OtagoPolytechnic/DunedinIoT/images/20160920_135408.jpg

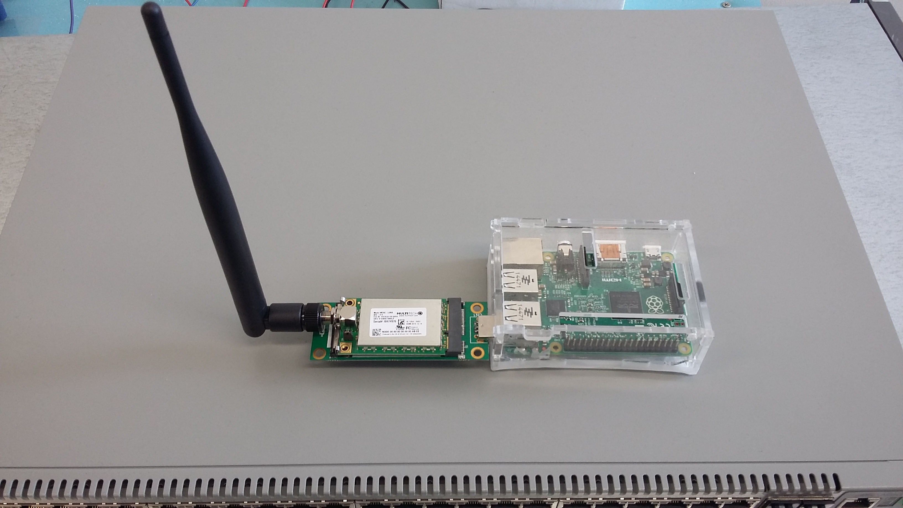
images/20160920_135408.jpg
