OtagoPolytechnic/DunedinIoT/images/20160920_135431.jpg

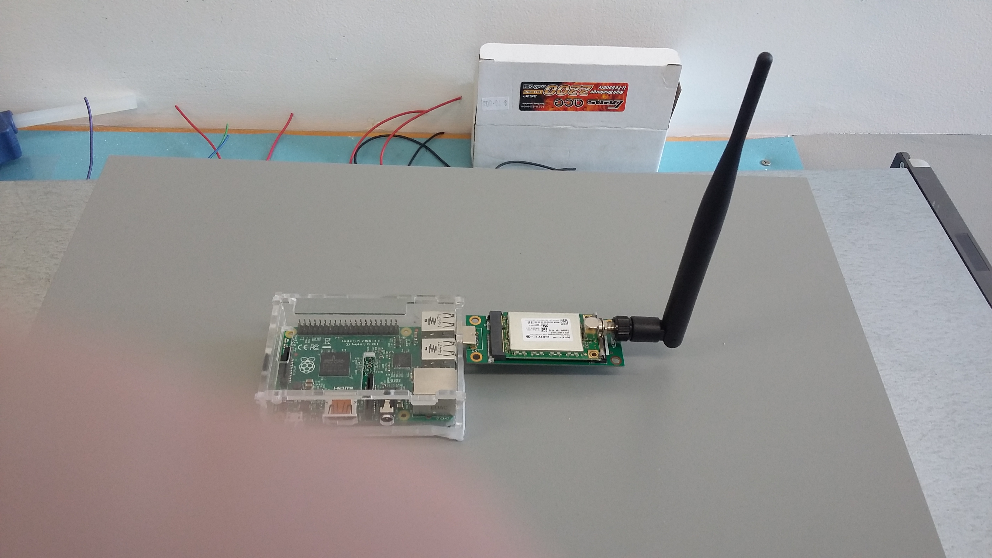
images/20160920_135431.jpg
