OtagoPolytechnic/DunedinIoT/images/20160920_135444.jpg

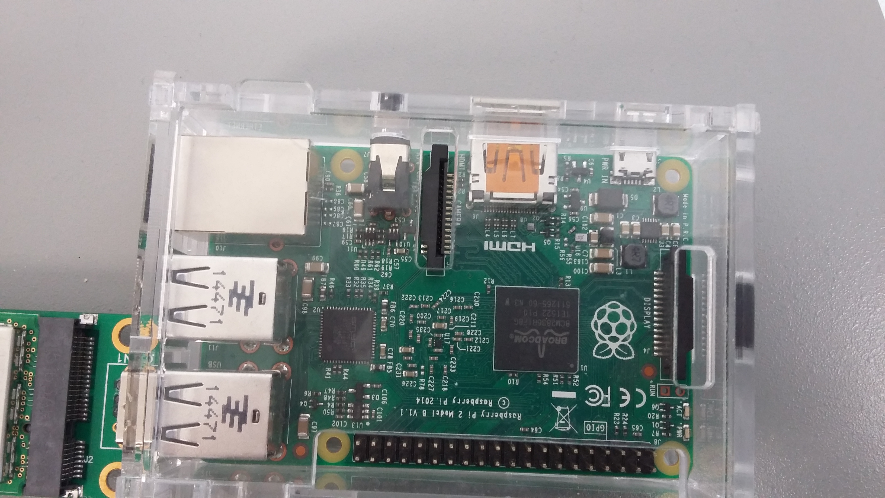
images/20160920_135444.jpg
