OtagoPolytechnic/DunedinIoT/images/20160920_135453.jpg

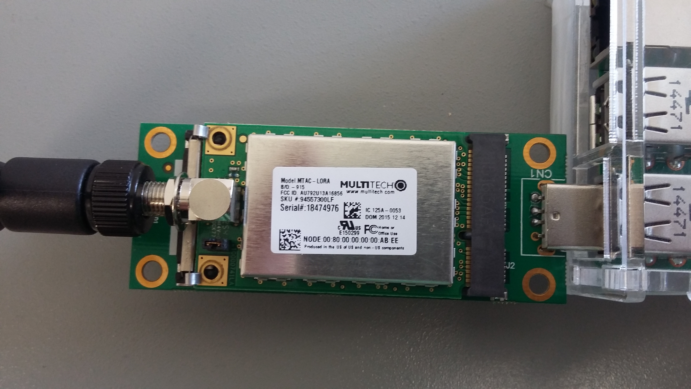
images/20160920_135453.jpg
