OtagoPolytechnic/DunedinIoT/images/20160920_135511.jpg

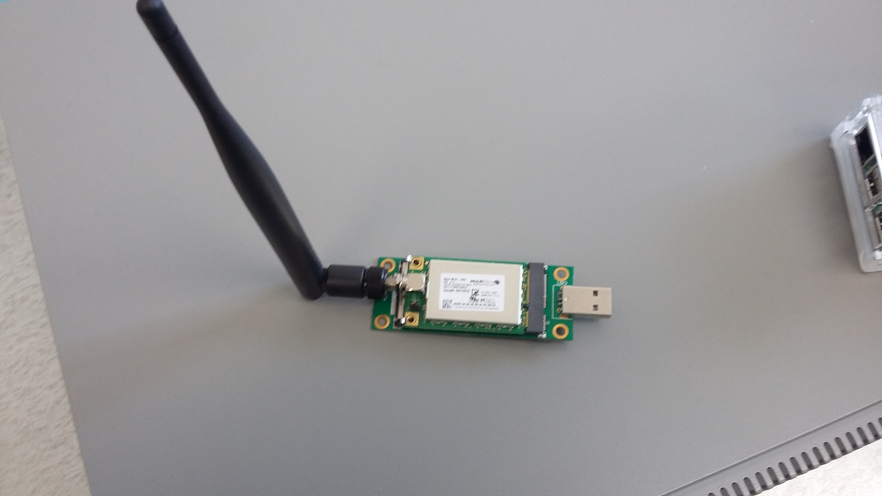
images/20160920_135511.jpg
