OtagoPolytechnic/DunedinIoT/images/20160920_135528.jpg

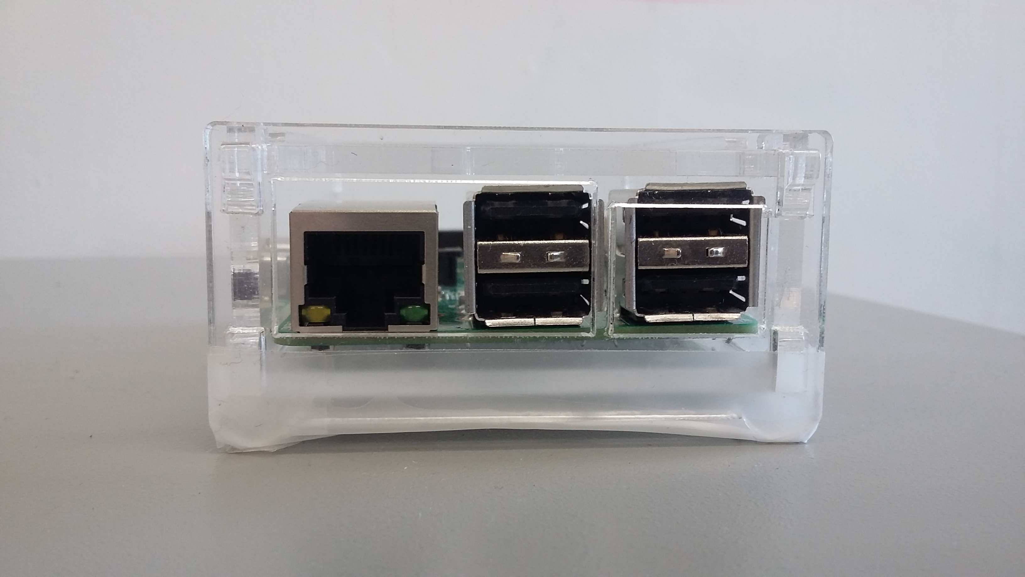
images/20160920_135528.jpg
