OtagoPolytechnic/DunedinIoT/images/background/1.jpg

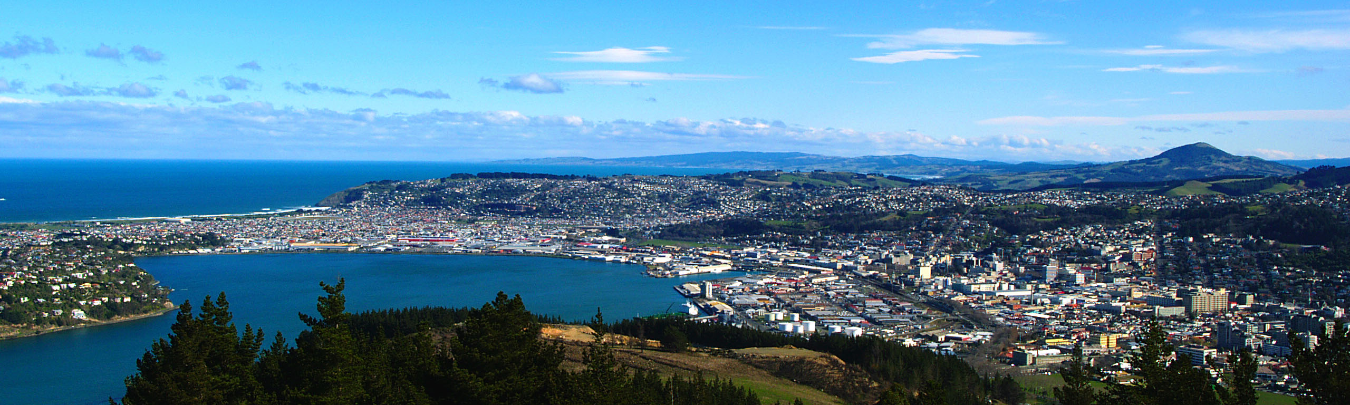
images/background/1.jpg
