OtagoPolytechnic/DunedinIoT/images/mini-pcie.jpg

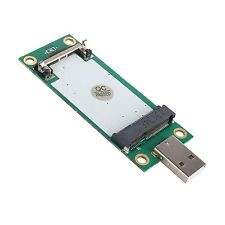
images/mini-pcie.jpg
