OtagoPolytechnic/DunedinIoT/images/raspberryPi.jpg

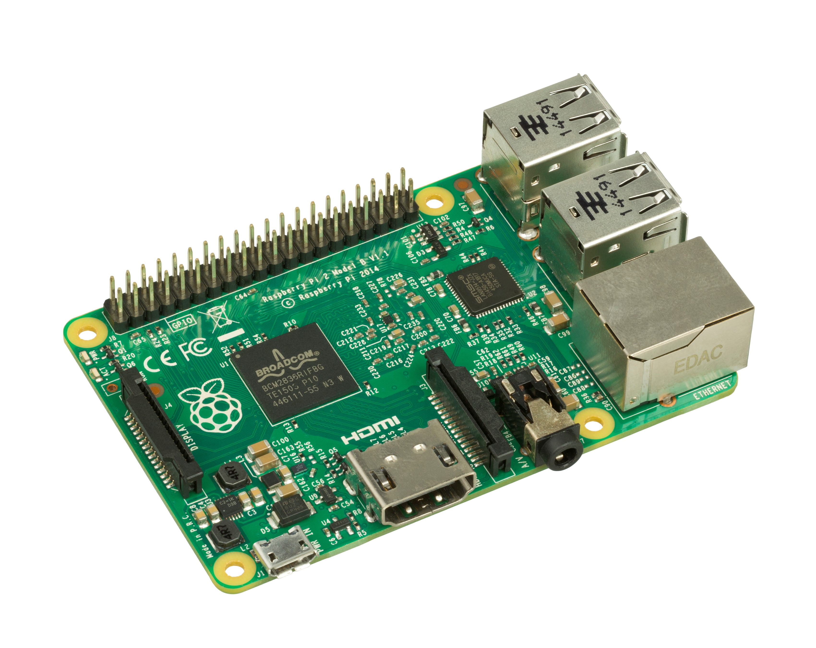
images/raspberryPi.jpg
