OtagoPolytechnic/DunedinIoT/images/whatyouneed.png

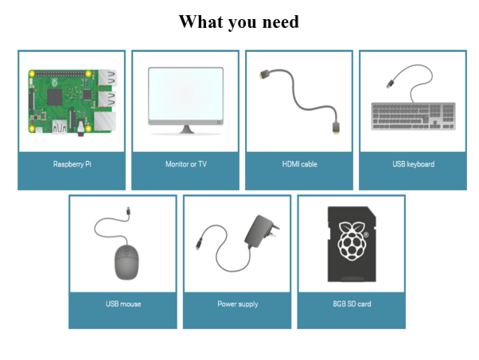
images/whatyouneed.png
